Mecuba/Flyfox/CAD/Flyfox - Ensamblaje Móvil con Servos/STEP Files/MG995_Gear2.STEP

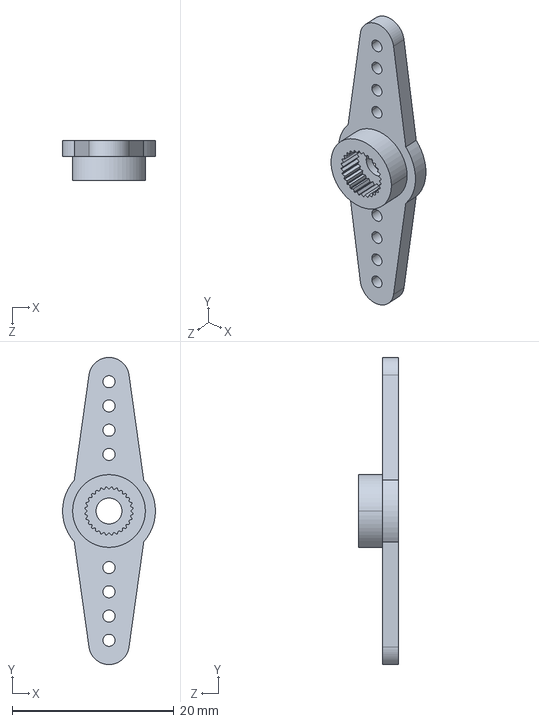
[picture p31: CAD file, 2022-05-17]
CAD/Flyfox - Ensamblaje Móvil con Servos/STEP Files/MG995_Gear2.STEP
11.5 x 38.0 x 5.00 mm
