Mecuba/Flyfox/CAD/PortaPowerBank_Cuadrado.SLDPRT

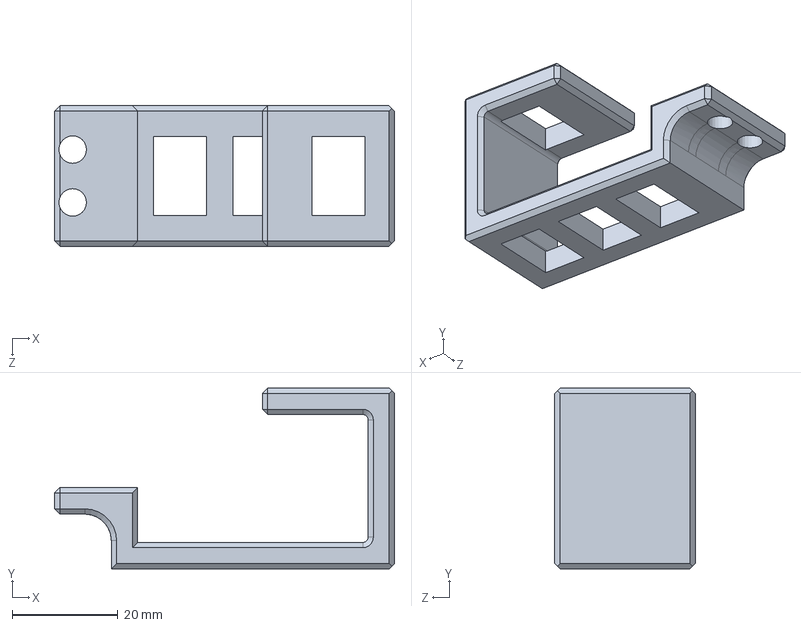
[picture p32: CAD file, 2022-05-12]
CAD/PortaPowerBank_Cuadrado.SLDPRT
64.3 x 34.2 x 26.6 mm
