Mecuba/Flyfox/CAD/STLs/flyfox para gravity sketch/flyfox - Servo Futaba S3003-0.step.STL

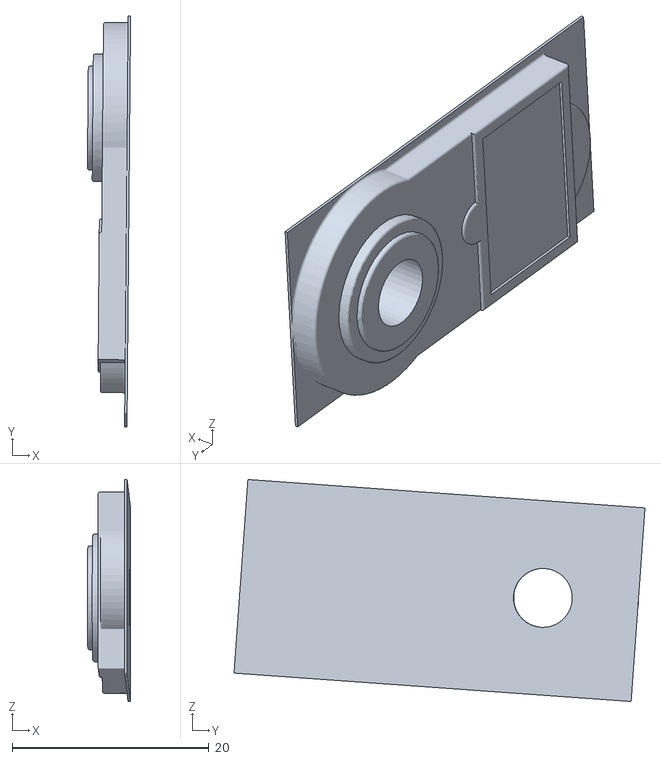
[picture p33: CAD file, 2022-03-08]
CAD/STLs/flyfox para gravity sketch/flyfox - Servo Futaba S3003-0.step.STL
4.40 x 41.8 x 22.6
