Mecuba/Flyfox/CAD/Flyfox - Ensamblaje Móvil con Servos/02 Pan/S20.002 Sujeta Servo Pan - PortaAccesorios.SLDPRT

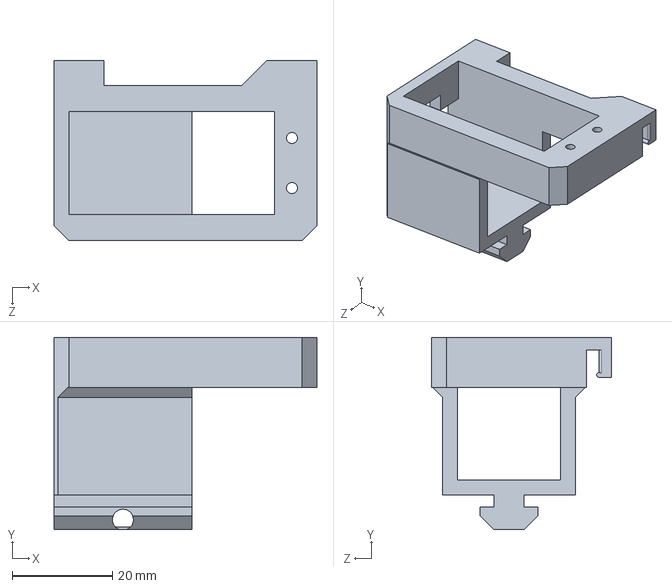
[picture p34: CAD file, 2022-05-17]
CAD/Flyfox - Ensamblaje Móvil con Servos/02 Pan/S20.002 Sujeta Servo Pan - PortaAccesorios.SLDPRT
52.5 x 38.4 x 36.0 mm
