Mecuba/Flyfox/CAD/Flyfox - Ensamblaje Móvil con Servos/STEP Files/servo mg995 horn 2 sides.step

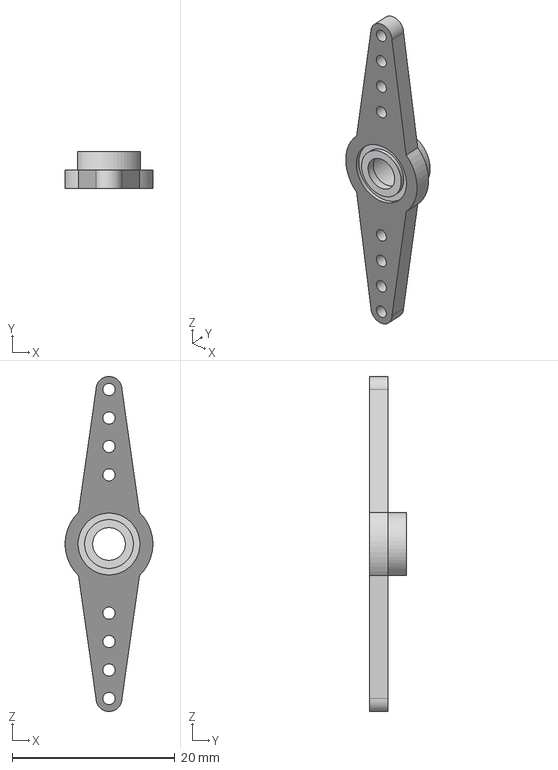
[picture p35: CAD file, 2022-05-12]
CAD/Flyfox - Ensamblaje Móvil con Servos/STEP Files/servo mg995 horn 2 sides.step
10.8 x 4.50 x 41.2 mm
