Mecuba/Flyfox/CAD/PowerBank-Cuadrado.SLDPRT

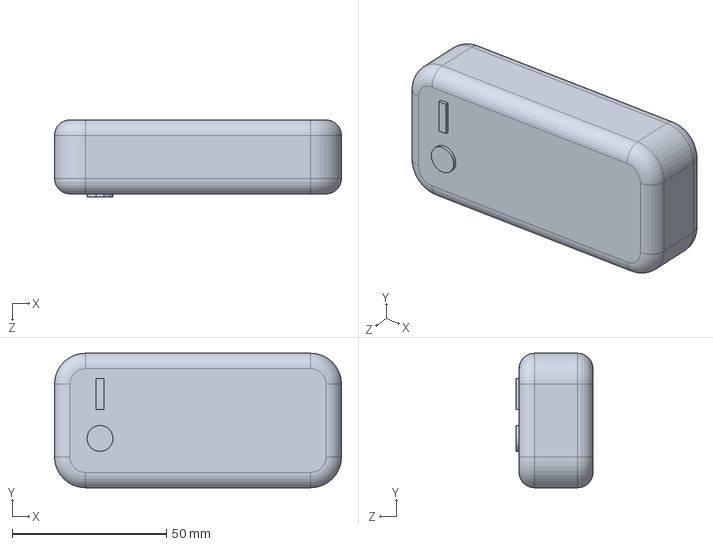
[picture p36: CAD file, 2022-03-08]
CAD/PowerBank-Cuadrado.SLDPRT
93.0 x 43.6 x 25.0 mm
