Mecuba/Flyfox/CAD/STLs/flyfox para gravity sketch/flyfox - RightArm.STL

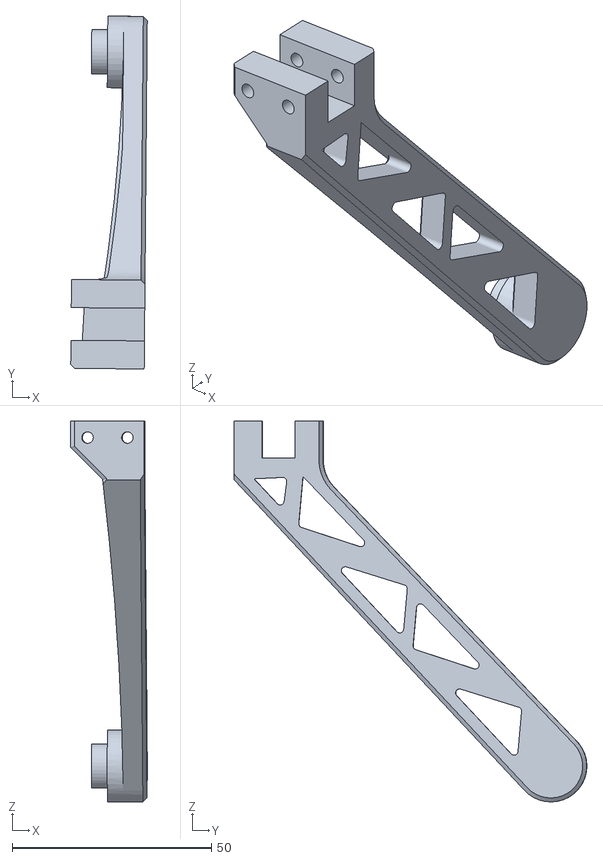
[picture p37: CAD file, 2022-03-08]
CAD/STLs/flyfox para gravity sketch/flyfox - RightArm.STL
19.2 x 88.6 x 95.6
