Mecuba/Flyfox/CAD/Flyfox - Ensamblaje Móvil con Servos/01 Flyfox Base/EMServoPolea.SLDPRT

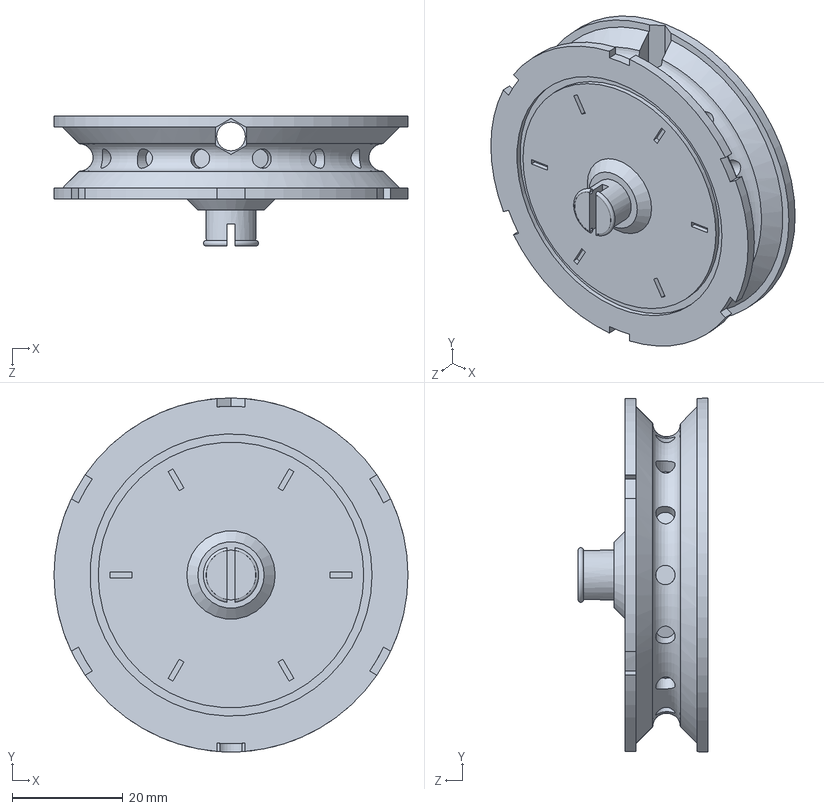
[picture p38: CAD file, 2022-05-17]
CAD/Flyfox - Ensamblaje Móvil con Servos/01 Flyfox Base/EMServoPolea.SLDPRT
64.0 x 64.0 x 23.5 mm
