Mecuba/Flyfox/CAD/Flyfox - Ensamblaje Móvil con Servos/STEP Files/servo Assem v2.step

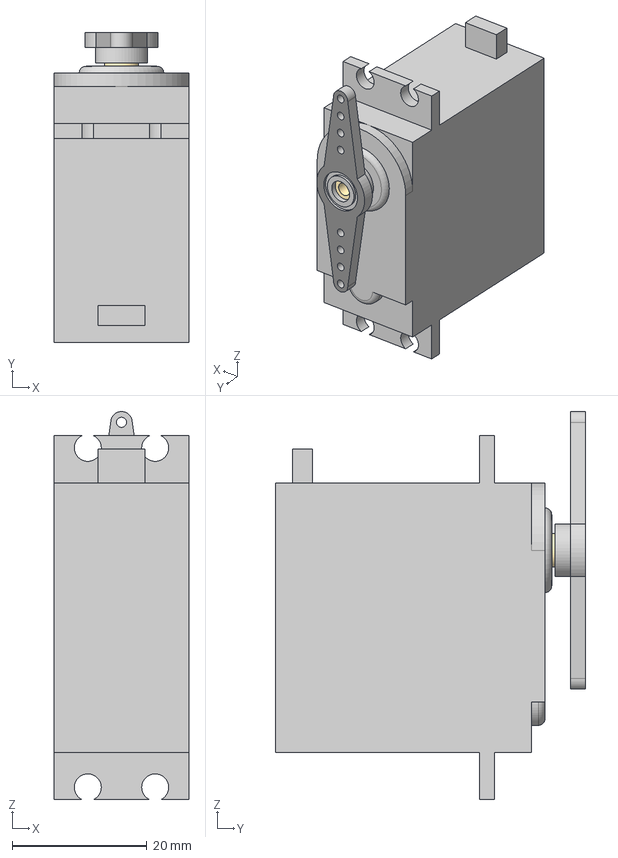
[picture p39: CAD file, 2022-05-12]
CAD/Flyfox - Ensamblaje Móvil con Servos/STEP Files/servo Assem v2.step
20.0 x 46.0 x 57.6 mm
servo strong junk 2
servo strong junk 1
