Mecuba/Flyfox/CAD/STLs/EMSlider-PortaAccesorios.STL

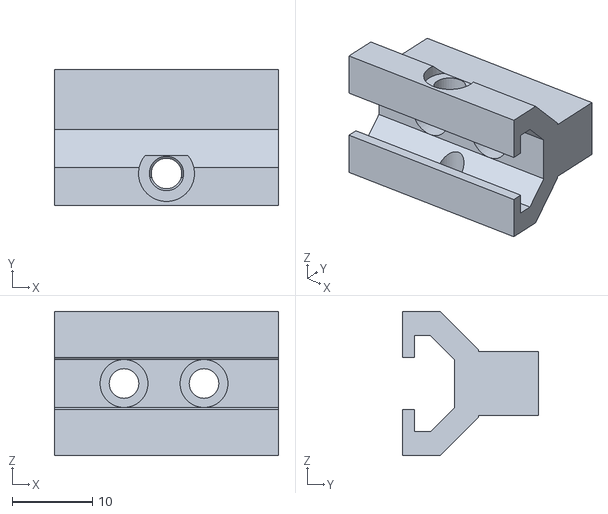
[picture p40: CAD file, 2022-05-17]
CAD/STLs/EMSlider-PortaAccesorios.STL
28.0 x 17.0 x 18.0
