Mecuba/Flyfox/CAD/STLs/flyfox para gravity sketch/flyfox - ServoPolea.STL

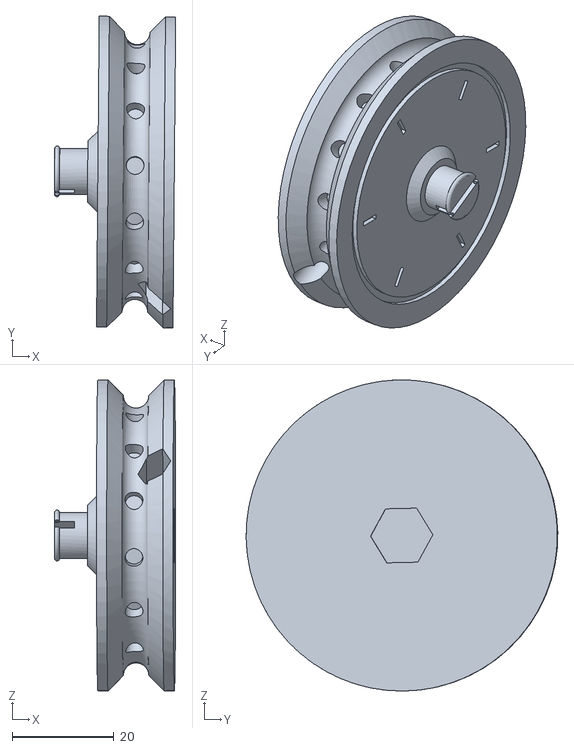
[picture p41: CAD file, 2022-03-08]
CAD/STLs/flyfox para gravity sketch/flyfox - ServoPolea.STL
23.8 x 61.1 x 61.0
