Mecuba/Flyfox/CAD/Accesorios/Finales de línea.SLDPRT

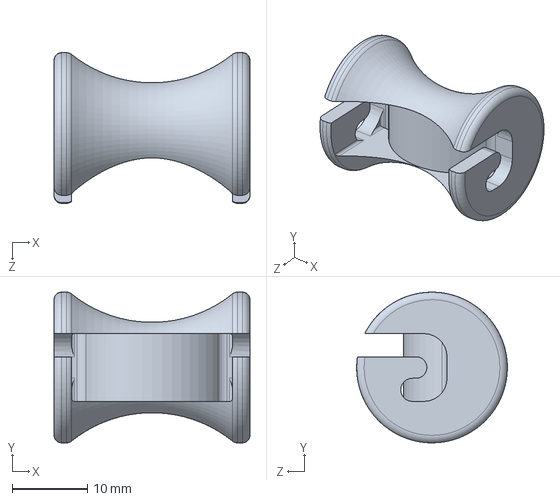
[picture p42: CAD file, 2022-02-02]
CAD/Accesorios/Finales de línea.SLDPRT
26.0 x 20.0 x 20.0 mm
