Mecuba/Flyfox/CAD/Flyfox - Ensamblaje Móvil con Servos/01 Flyfox Base/EMSlider-PortaAccesorios.SLDPRT

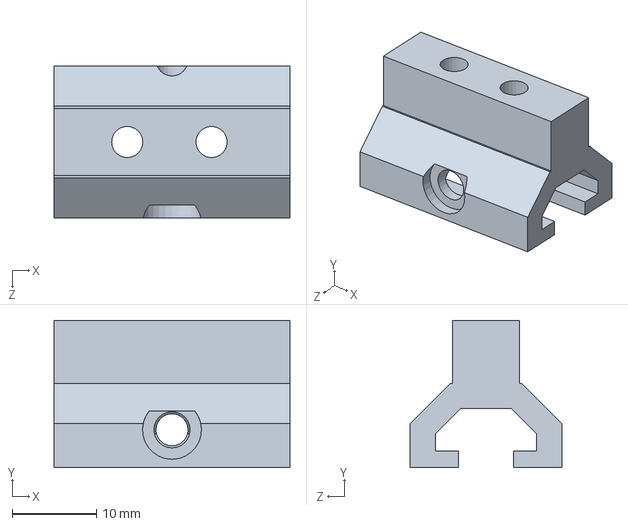
[picture p43: CAD file, 2022-05-17]
CAD/Flyfox - Ensamblaje Móvil con Servos/01 Flyfox Base/EMSlider-PortaAccesorios.SLDPRT
28.0 x 17.5 x 18.0 mm
