Mecuba/Flyfox/CAD/Flyfox - Ensamblaje Móvil con Servos/STEP Files/MG995.STEP

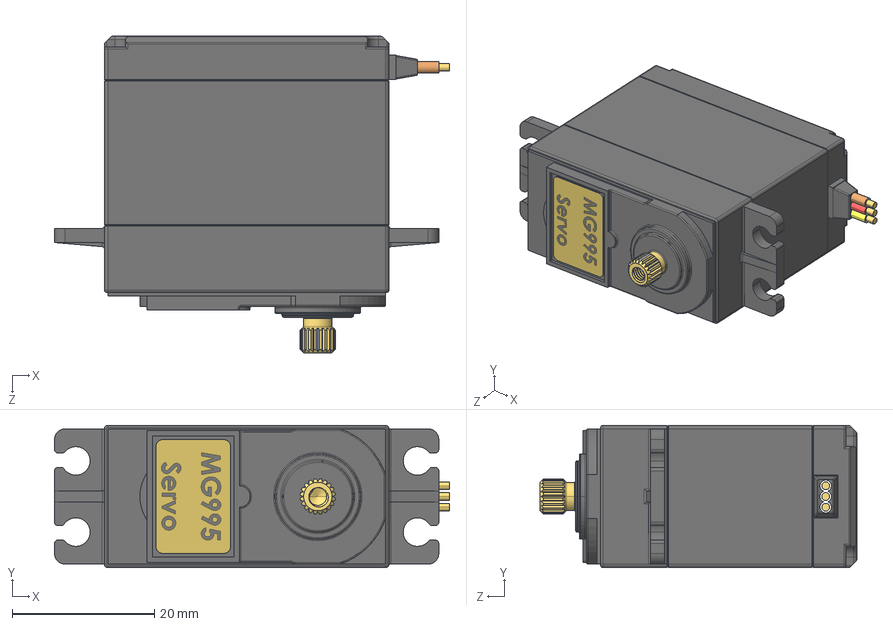
[picture p44: CAD file, 2022-05-12]
CAD/Flyfox - Ensamblaje Móvil con Servos/STEP Files/MG995.STEP
55.5 x 20.0 x 44.5 mm
