Mecuba/Flyfox/CAD/STLs/flyfox para gravity sketch/flyfox - BastidorCentral.STL

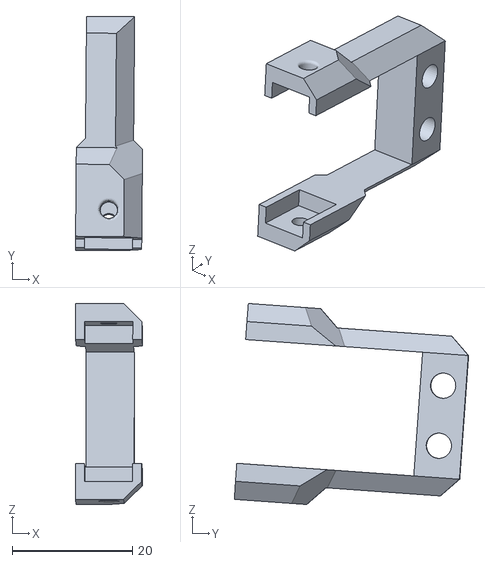
[picture p45: CAD file, 2022-03-08]
CAD/STLs/flyfox para gravity sketch/flyfox - BastidorCentral.STL
11.1 x 38.9 x 33.4
