Mecuba/Flyfox/CAD/PortaPowerBank_Duracell.SLDPRT

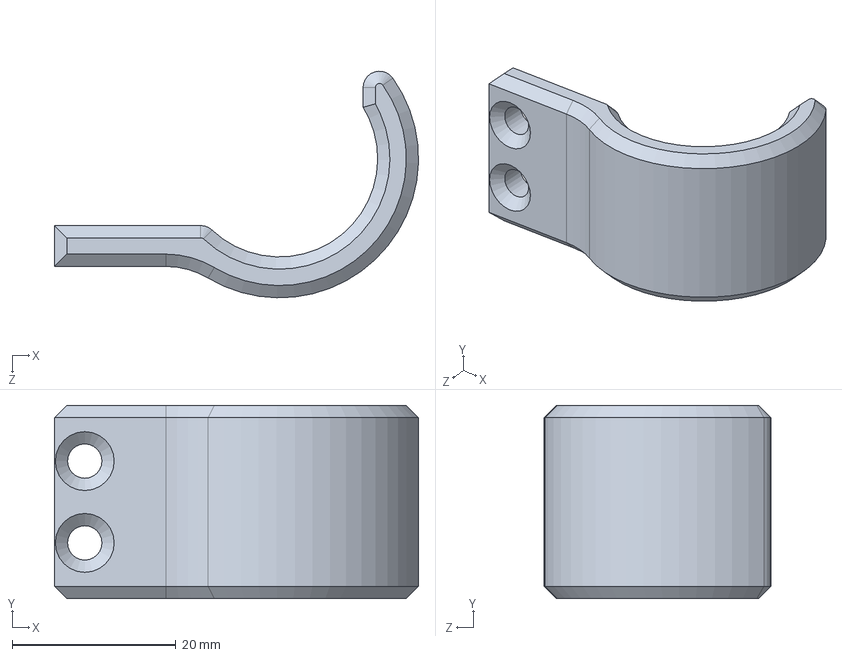
[picture p46: CAD file, 2022-03-08]
CAD/PortaPowerBank_Duracell.SLDPRT
44.5 x 23.6 x 27.7 mm
