Mecuba/Flyfox/CAD/STLs/flyfox para gravity sketch/flyfox - MG995.step.STL

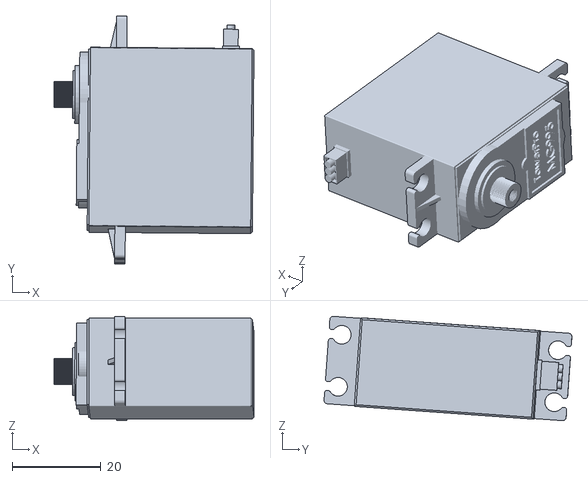
[picture p47: CAD file, 2022-03-08]
CAD/STLs/flyfox para gravity sketch/flyfox - MG995.step.STL
45.0 x 55.8 x 23.5
