Mecuba/Flyfox/CAD/STLs/flyfox.3MF

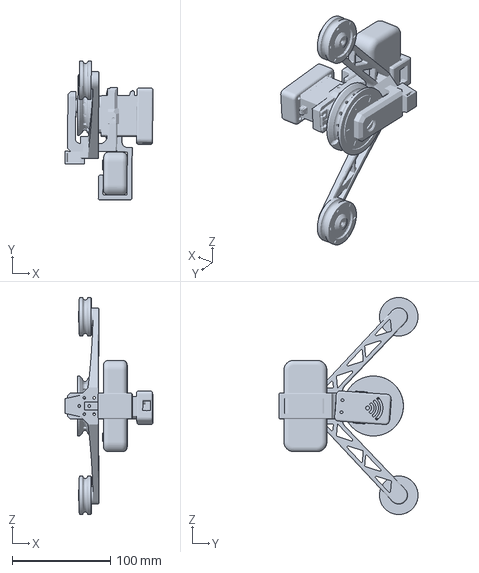
[picture p48: CAD file, 2022-03-08]
CAD/STLs/flyfox.3MF
89.5 x 141.5 x 220.7 mm
