Mecuba/Flyfox/CAD/Flyfox - Ensamblaje Móvil con Servos/STEP Files/phone_holder.stp

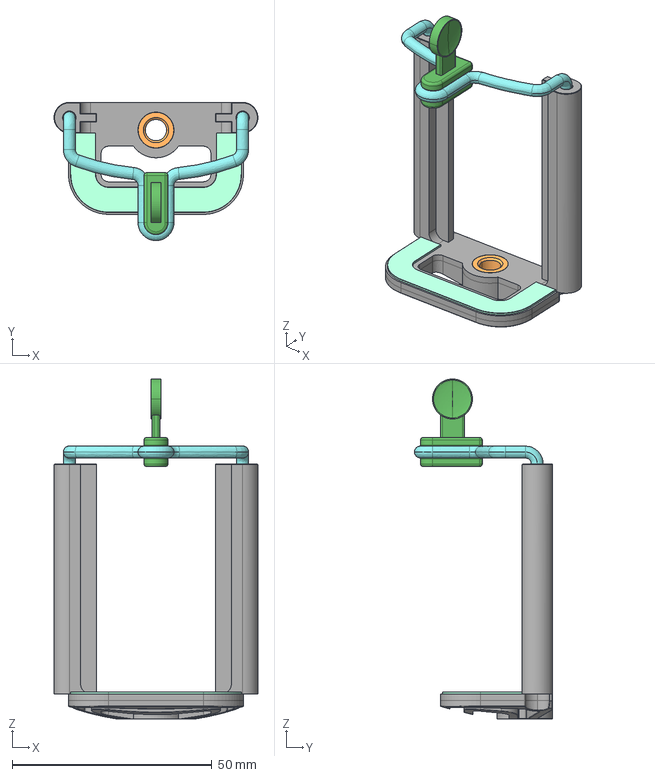
[picture p49: CAD file, 2022-01-31]
CAD/Flyfox - Ensamblaje Móvil con Servos/STEP Files/phone_holder.stp
51.0 x 34.6 x 85.0 mm
