Mecuba/Flyfox/CAD/PiezaFabrizz.SLDPRT

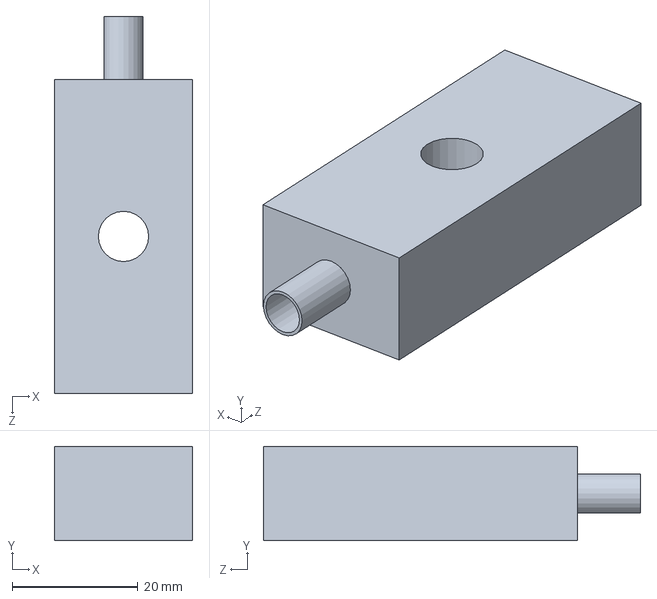
[picture p50: CAD file, 2022-02-04]
CAD/PiezaFabrizz.SLDPRT
22.0 x 15.0 x 60.0 mm
