Mecuba/Flyfox/CAD/STLs/flyfox para gravity sketch/flyfox - Bottom.step.STL

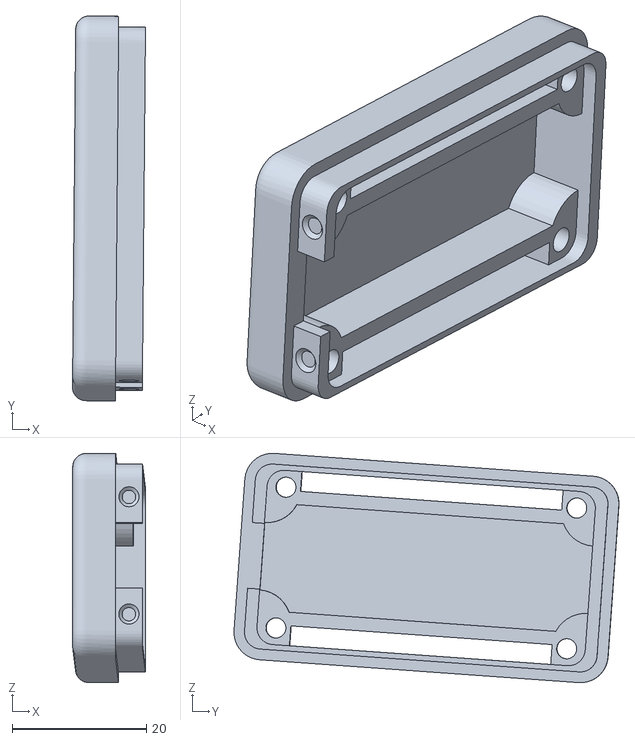
[picture p51: CAD file, 2022-03-08]
CAD/STLs/flyfox para gravity sketch/flyfox - Bottom.step.STL
10.9 x 57.3 x 34.1
