Mecuba/Flyfox/CAD/STLs/LeftArm.STL

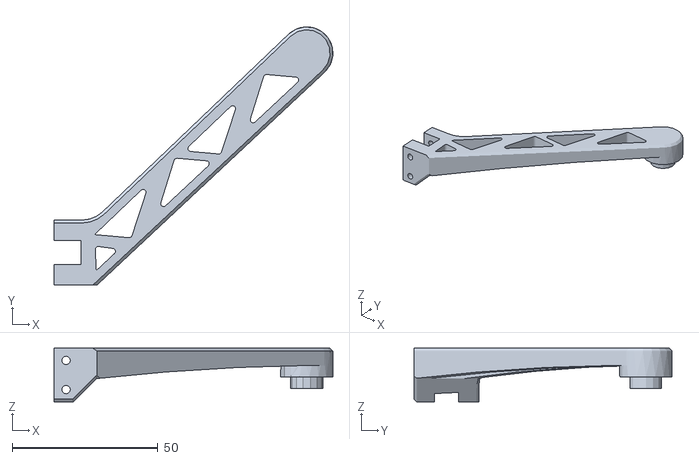
[picture p52: CAD file, 2022-01-31]
CAD/STLs/LeftArm.STL
95.6 x 88.5 x 18.5
