Mecuba/Flyfox/CAD/Flyfox - Ensamblaje Móvil con Servos/01 Flyfox Base/EMRodamientoRin.SLDPRT

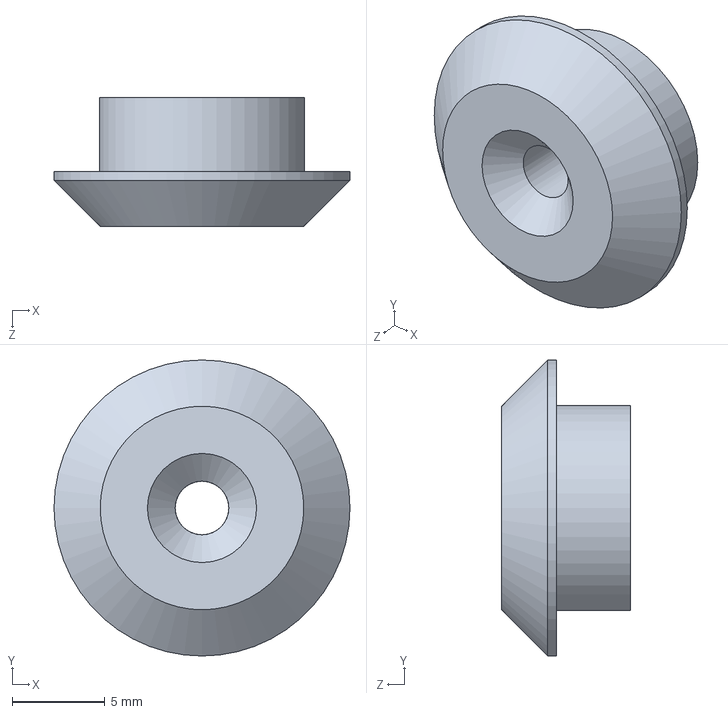
[picture p53: CAD file, 2022-05-12]
CAD/Flyfox - Ensamblaje Móvil con Servos/01 Flyfox Base/EMRodamientoRin.SLDPRT
16.0 x 16.0 x 7.00 mm
