Mecuba/Flyfox/CAD/STLs/BastidorCentral_Bottom.STL

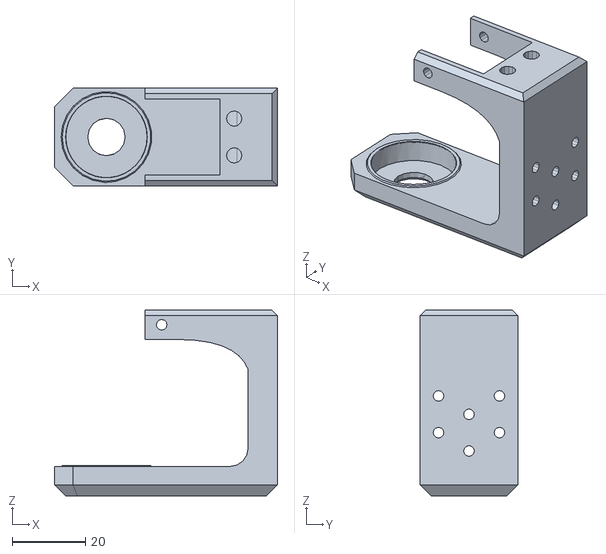
[picture p54: CAD file, 2022-01-31]
CAD/STLs/BastidorCentral_Bottom.STL
60.7 x 26.6 x 50.6
