Mecuba/Flyfox/CAD/STLs/flyfox para gravity sketch/flyfox - Servo Futaba S3003-1.step.STL

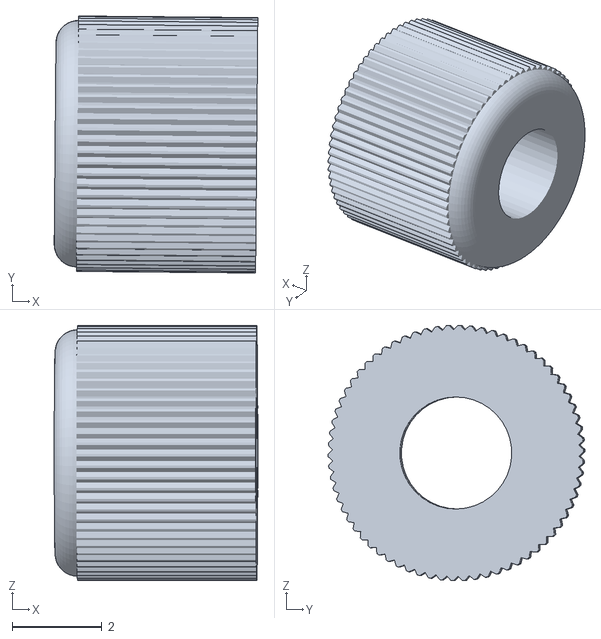
[picture p55: CAD file, 2022-03-08]
CAD/STLs/flyfox para gravity sketch/flyfox - Servo Futaba S3003-1.step.STL
4.54 x 5.73 x 5.70
