Mecuba/Flyfox/CAD/STLs/BastidorCentral_Top.STL

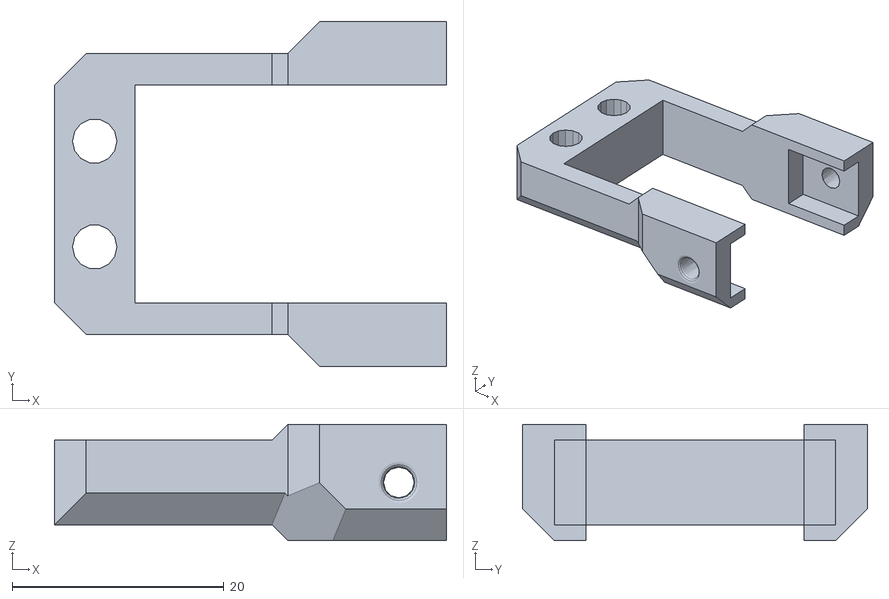
[picture p56: CAD file, 2022-01-31]
CAD/STLs/BastidorCentral_Top.STL
37.0 x 32.6 x 11.0
