Mecuba/Flyfox/CAD/STLs/flyfox para gravity sketch/flyfox - PortaAccesorios.STL

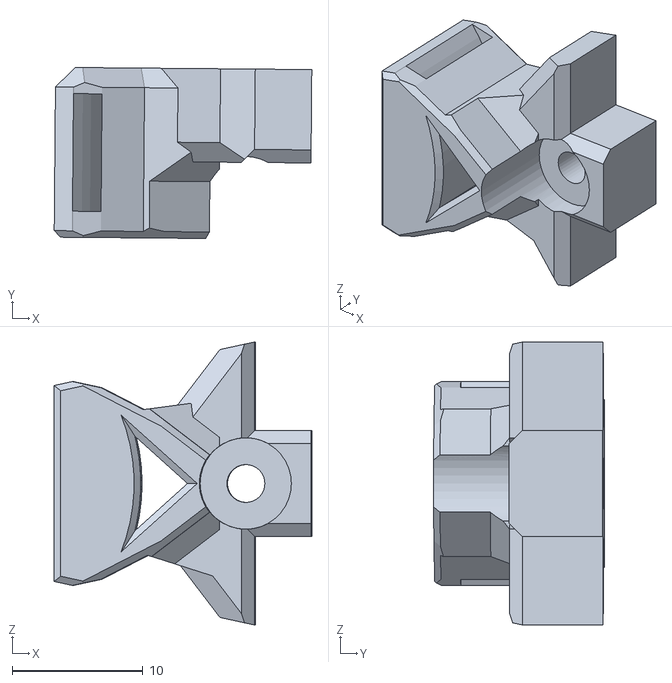
[picture p57: CAD file, 2022-03-08]
CAD/STLs/flyfox para gravity sketch/flyfox - PortaAccesorios.STL
19.7 x 13.1 x 21.7
