Mecuba/Flyfox/CAD/Flyfox - Ensamblaje Móvil con Servos/01 Flyfox Base/EMRodamientoSuit.sldprt

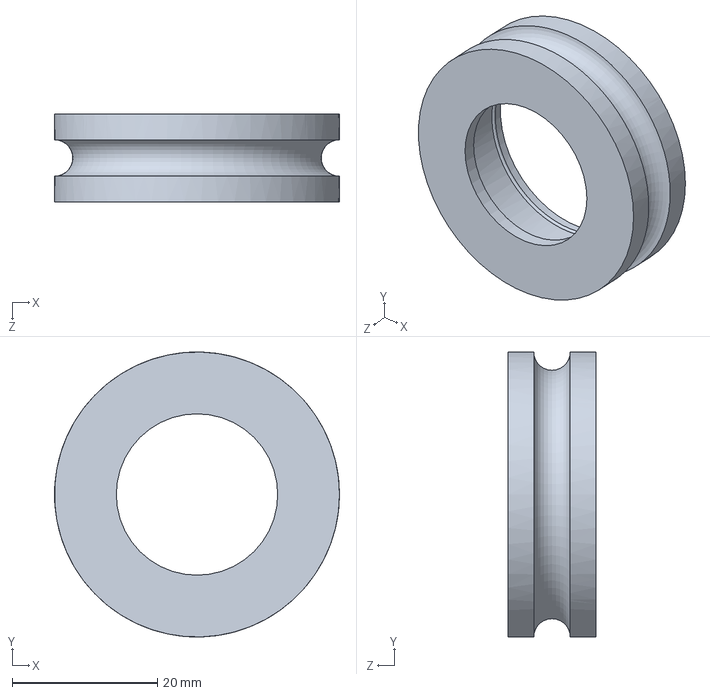
[picture p58: CAD file, 2022-05-12]
CAD/Flyfox - Ensamblaje Móvil con Servos/01 Flyfox Base/EMRodamientoSuit.sldprt
39.2 x 39.2 x 12.1 mm
