Mecuba/Flyfox/CAD/STLs/flyfox para gravity sketch/flyfox - FutabaS3003_AxisFix.STL

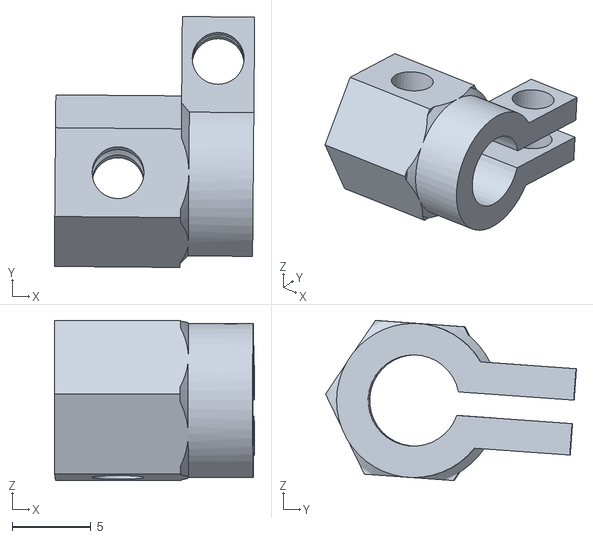
[picture p59: CAD file, 2022-03-08]
CAD/STLs/flyfox para gravity sketch/flyfox - FutabaS3003_AxisFix.STL
12.7 x 16.0 x 10.2
