Mecuba/Flyfox/CAD/Flyfox - Ensamblaje Móvil con Servos/01 Flyfox Base/EMRodamiento28x11.5x8.SLDPRT

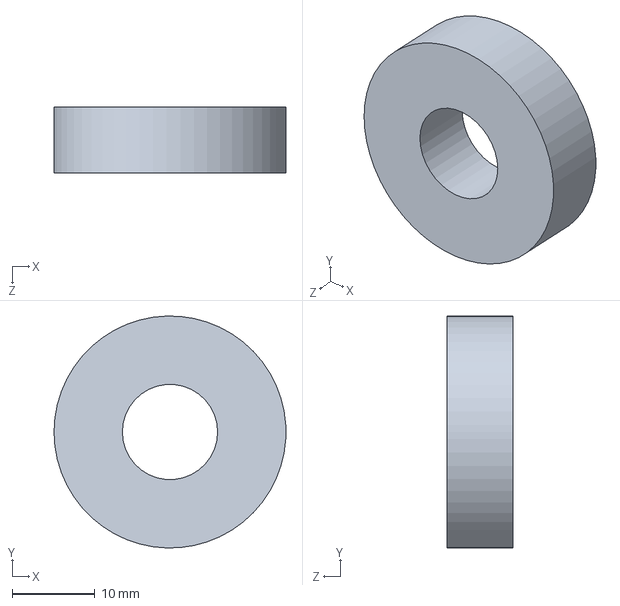
[picture p60: CAD file, 2022-05-12]
CAD/Flyfox - Ensamblaje Móvil con Servos/01 Flyfox Base/EMRodamiento28x11.5x8.SLDPRT
28.0 x 28.0 x 8.00 mm
