Mecuba/Flyfox/CAD/Flyfox - Ensamblaje Móvil con Servos/01 Flyfox Base/EMFutabaS3003_AxisFix.SLDPRT

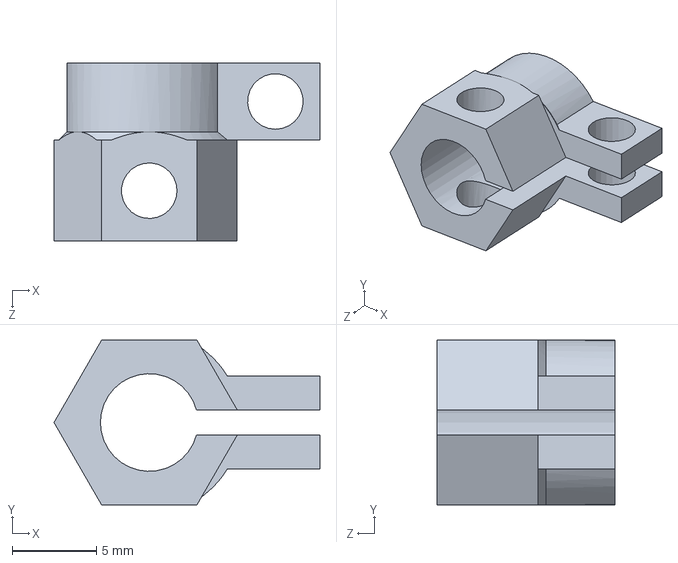
[picture p61: CAD file, 2022-05-12]
CAD/Flyfox - Ensamblaje Móvil con Servos/01 Flyfox Base/EMFutabaS3003_AxisFix.SLDPRT
15.8 x 9.80 x 10.6 mm
