Mecuba/Flyfox/CAD/STLs/flyfox para gravity sketch/flyfox - PortaPowerBank_Cuadrado.STL

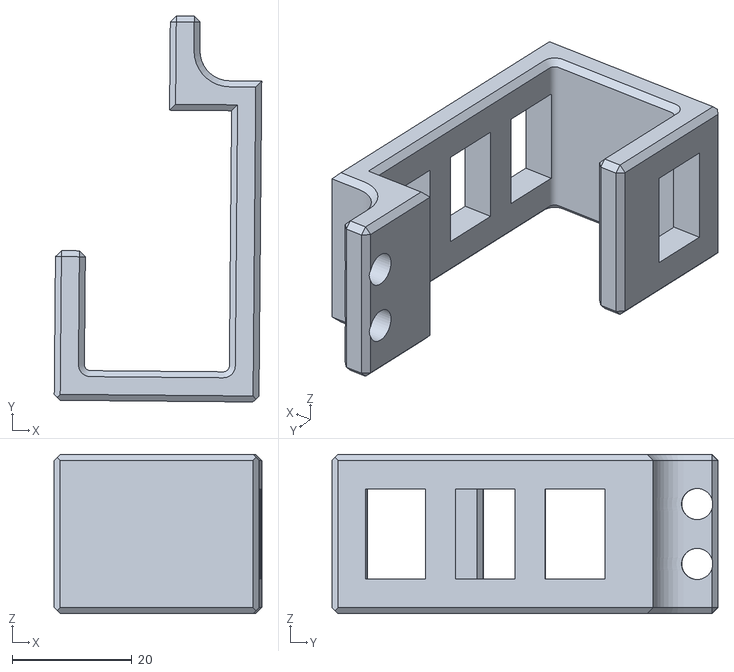
[picture p62: CAD file, 2022-03-08]
CAD/STLs/flyfox para gravity sketch/flyfox - PortaPowerBank_Cuadrado.STL
34.7 x 64.5 x 26.6
