Mecuba/Flyfox/CAD/STLs/flyfox para gravity sketch/flyfox - Rodamiento28x11.5x8.STL

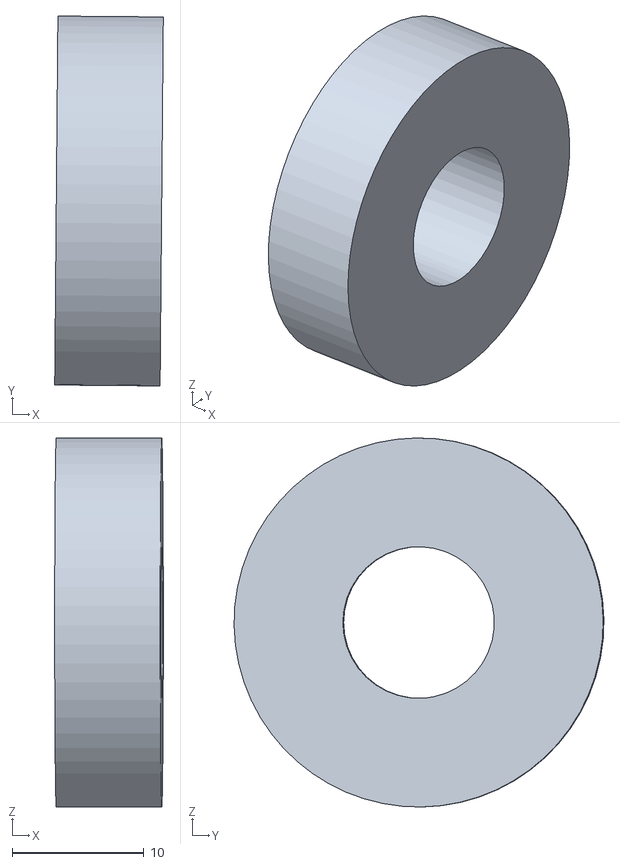
[picture p63: CAD file, 2022-03-08]
CAD/STLs/flyfox para gravity sketch/flyfox - Rodamiento28x11.5x8.STL
8.24 x 28.1 x 28.0
