Mecuba/Flyfox/CAD/PowerBank-Dummy.SLDPRT

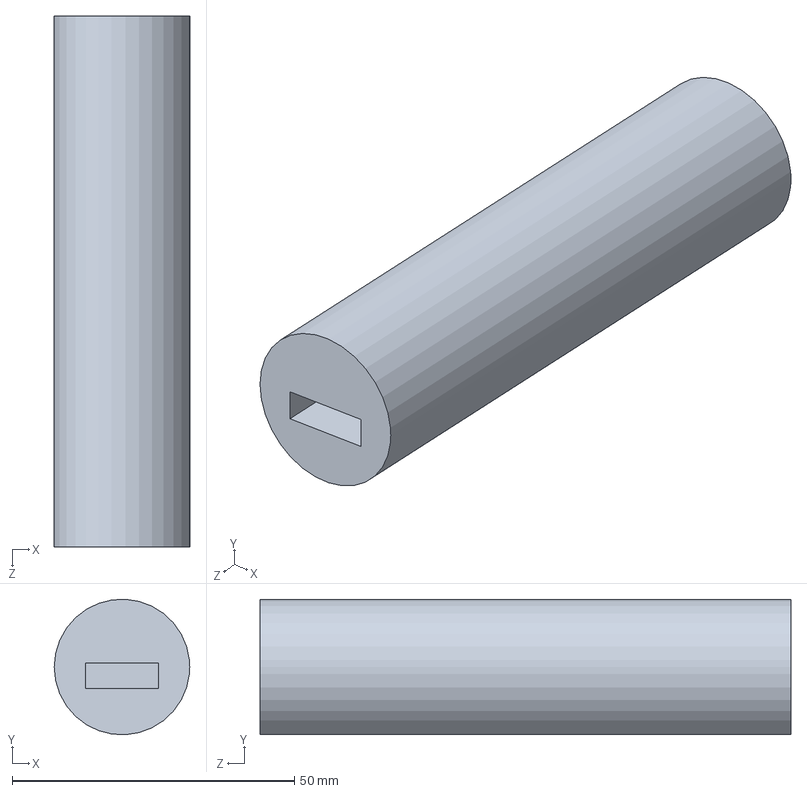
[picture p64: CAD file, 2022-01-31]
CAD/PowerBank-Dummy.SLDPRT
24.0 x 24.0 x 94.0 mm
