Mecuba/Flyfox/CAD/STLs/flyfox para gravity sketch/flyfox - Servo Futaba S3003.step.STL

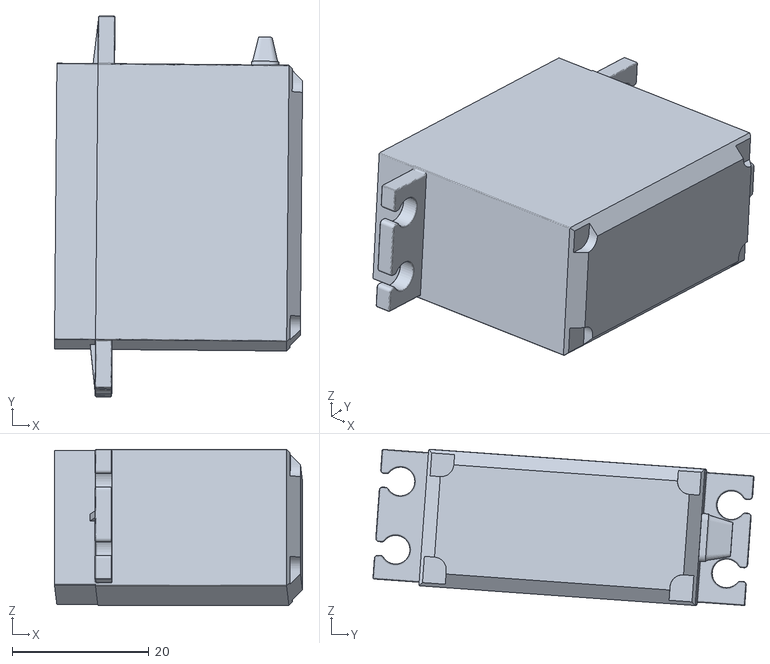
[picture p65: CAD file, 2022-03-08]
CAD/STLs/flyfox para gravity sketch/flyfox - Servo Futaba S3003.step.STL
36.3 x 55.7 x 22.8
