Mecuba/Flyfox/CAD/STLs/flyfox para gravity sketch/flyfox - RodamientoRin.STL

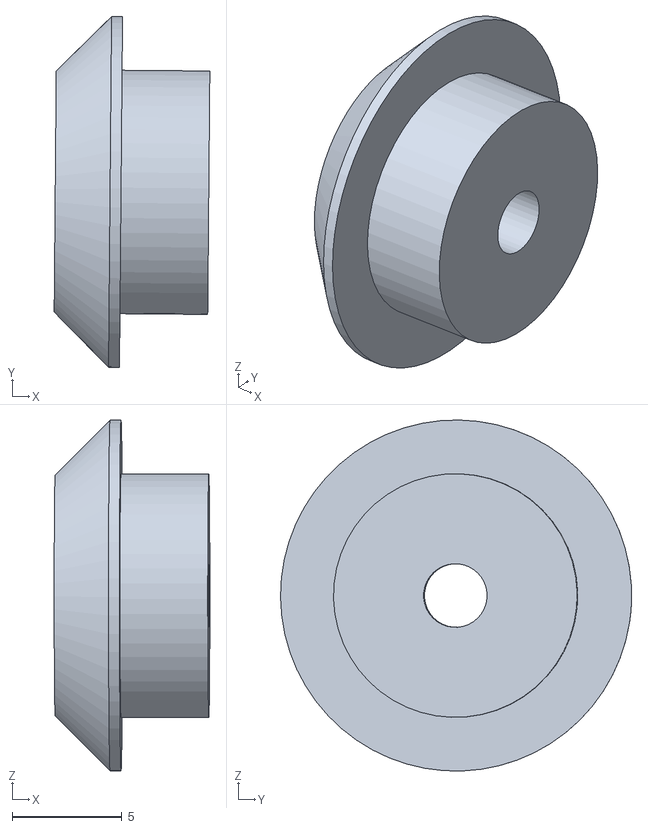
[picture p66: CAD file, 2022-03-08]
CAD/STLs/flyfox para gravity sketch/flyfox - RodamientoRin.STL
7.10 x 16.0 x 16.0
