Mecuba/Flyfox/CAD/STLs/flyfox para gravity sketch/flyfox - Top.step.STL

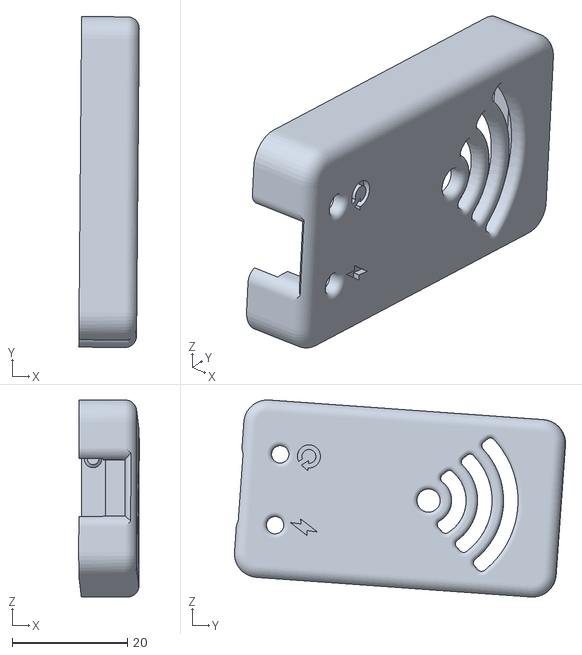
[picture p67: CAD file, 2022-03-08]
CAD/STLs/flyfox para gravity sketch/flyfox - Top.step.STL
10.5 x 57.3 x 34.1
