Mecuba/Flyfox/CAD/Superior.step.SLDPRT

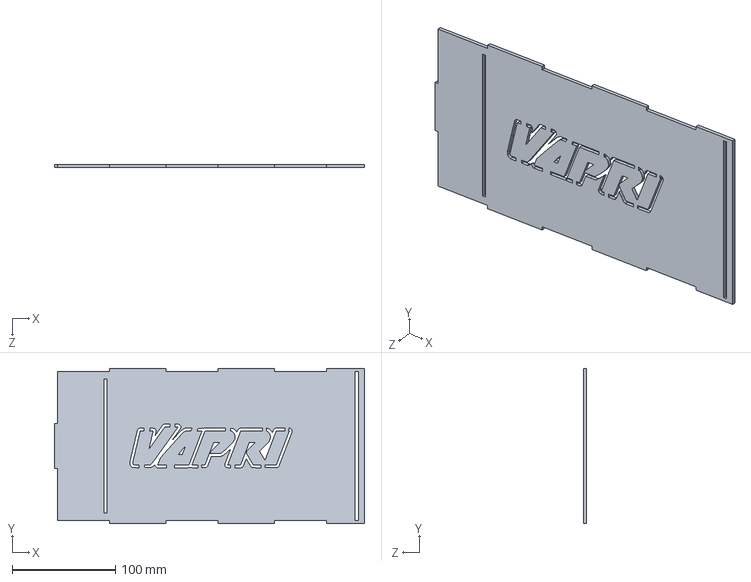
[picture p68: CAD file, 2022-01-31]
CAD/Superior.step.SLDPRT
300.0 x 150.0 x 3.00 mm
