Mecuba/Flyfox/CAD/pocophone.obj

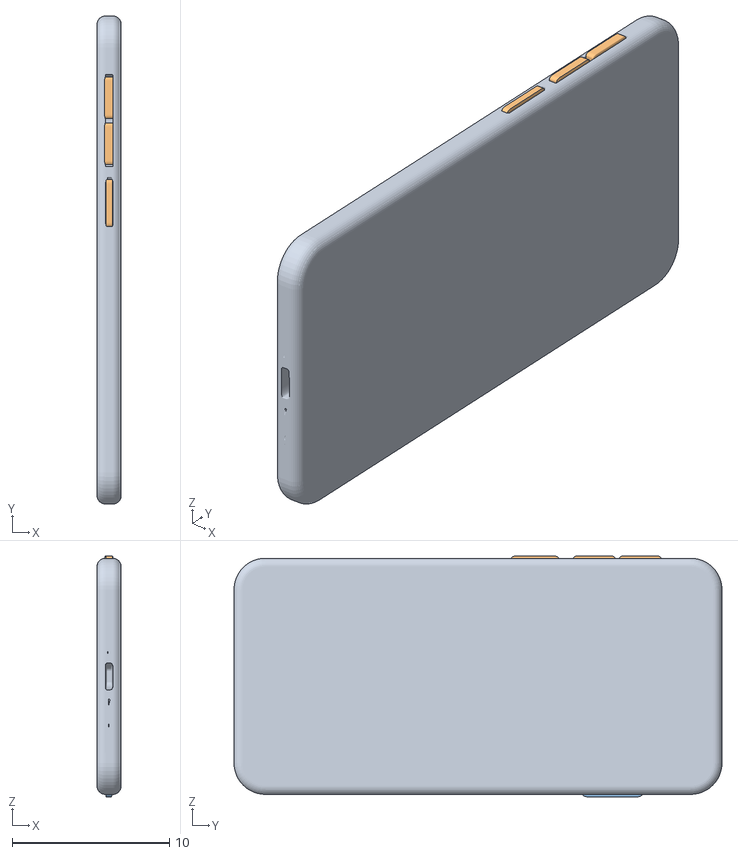
[picture p69: CAD file, 2022-01-31]
CAD/pocophone.obj
1.55 x 31.0 x 15.3
Cube.005_Cube.004
Notch_Cube.007
