Mecuba/Flyfox/CAD/Gopro Hero 3+.SLDPRT

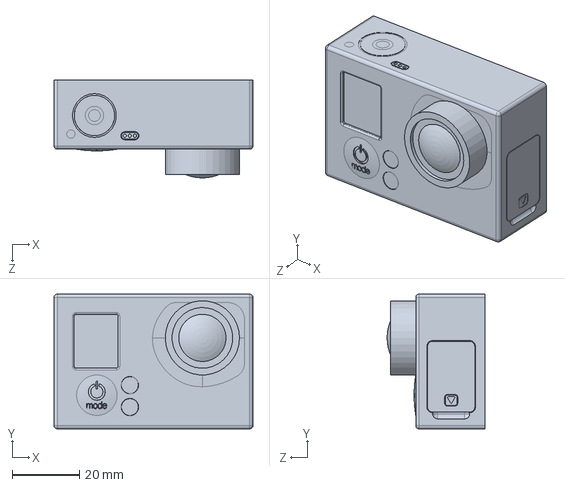
[picture p70: CAD file, 2022-01-31]
CAD/Gopro Hero 3+.SLDPRT
59.0 x 40.0 x 29.0 mm
