Mecuba/Flyfox/Código/Esp_Server_AP_WiFi (Qba)/socket_client.py

import websocket
ws = websocket.WebSocket()
ws.connect("ws://192.168.100.82:81")
print("Connected to WebSocket server")

# Ask the user for some input and transmit it
str = input("Say something: ")
ws.send(str)

# Wait for server to respond and print it
result = ws.recv()
print("Received: " + result)

# Gracefully close WebSocket connection
